ts-manuel/iMX6-Demo-Board/doc/MicroSD/2306141351_G-Switch-GT-TF003-H0185-01_C5155563.pdf

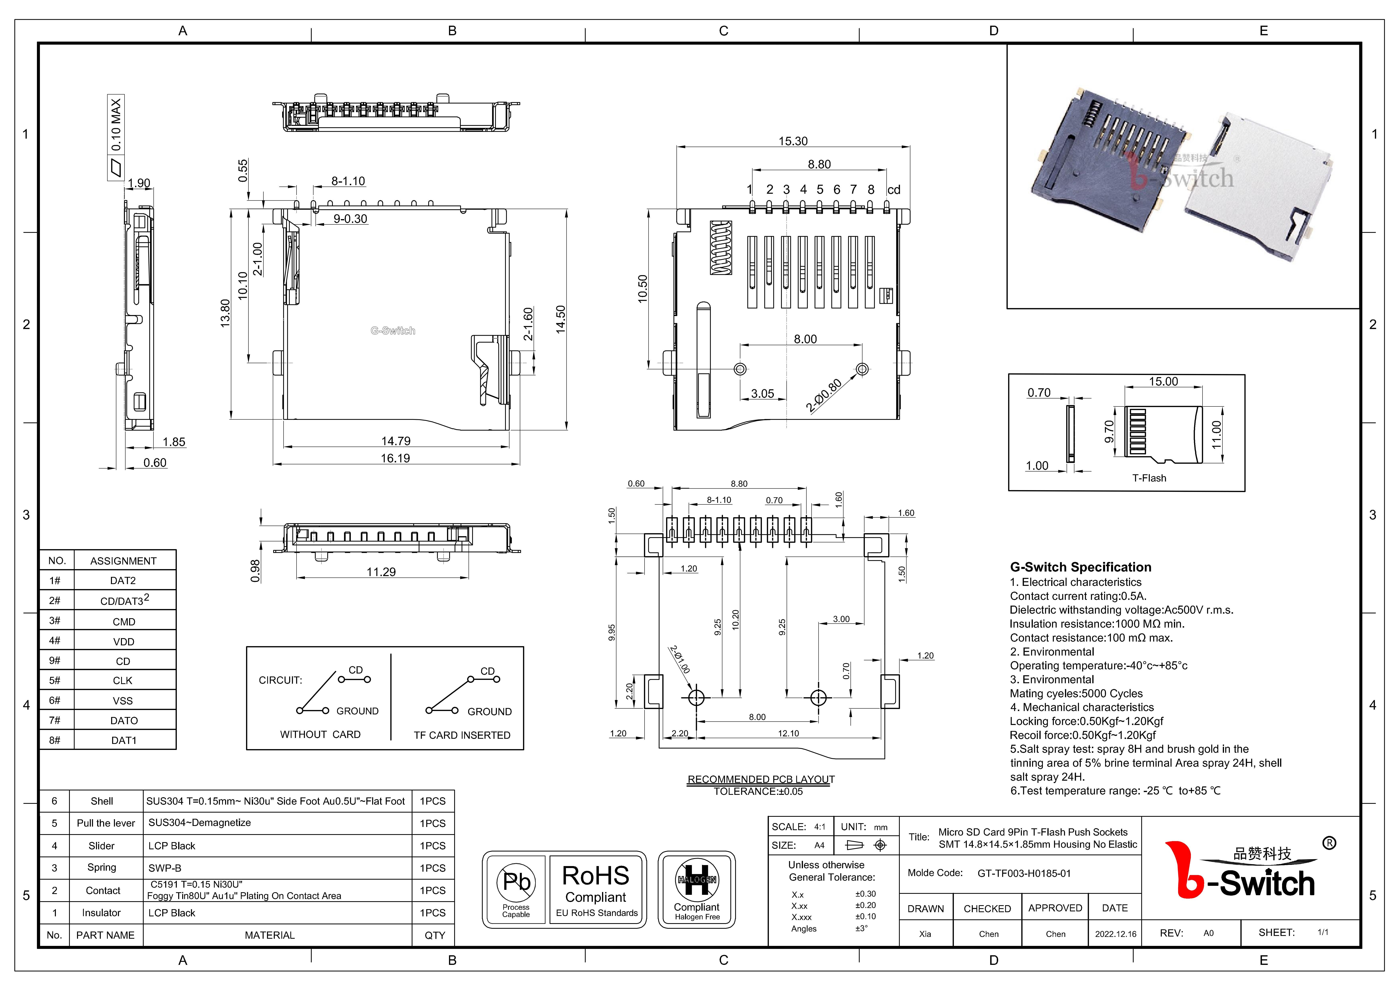
[picture p15: page 1]
