ts-manuel/iMX6-Demo-Board/doc/LCD/Alto.PNG

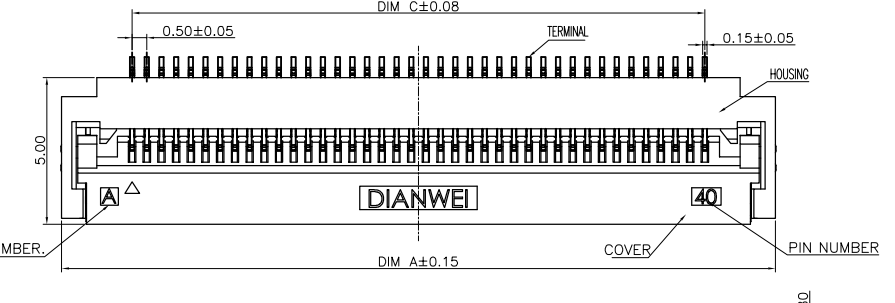
doc/LCD/Alto.PNG
