ts-manuel/iMX6-Demo-Board/doc/LCD/Basso.PNG

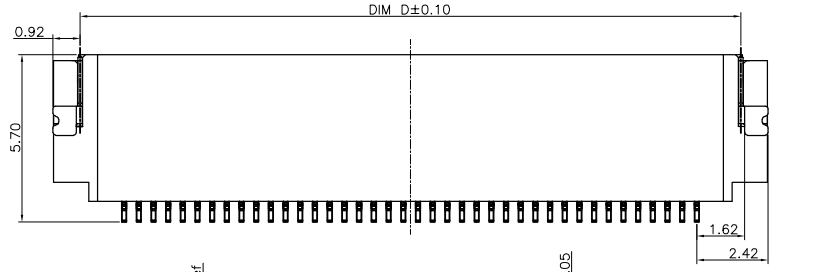
doc/LCD/Basso.PNG
