ts-manuel/iMX6-Demo-Board/kicad/images/BOOT_CONFIG.png

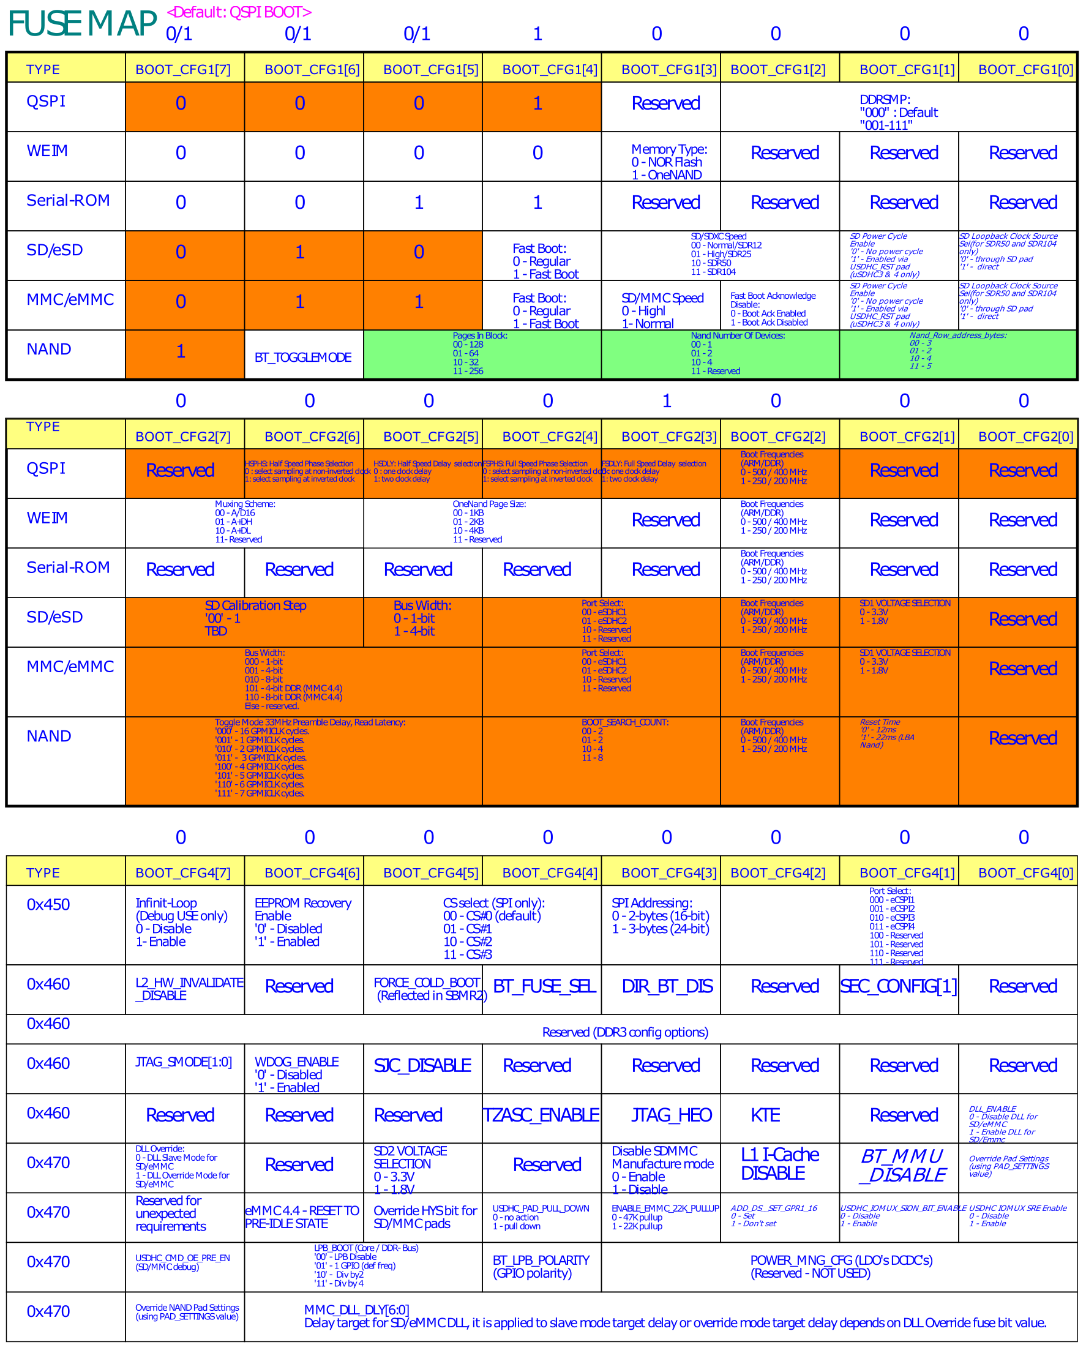
kicad/images/BOOT_CONFIG.png
