ts-manuel/iMX6-Demo-Board/kicad/images/BOOT_MODE.png

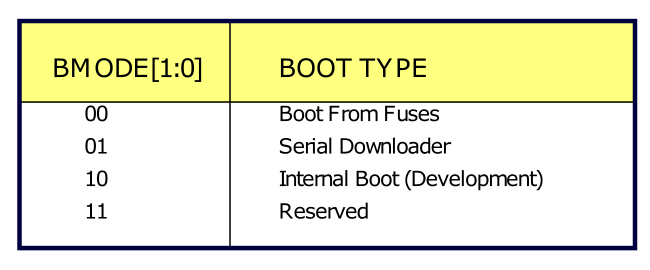
kicad/images/BOOT_MODE.png
