ts-manuel/iMX6-Demo-Board/kicad/images/BOTTOM.png

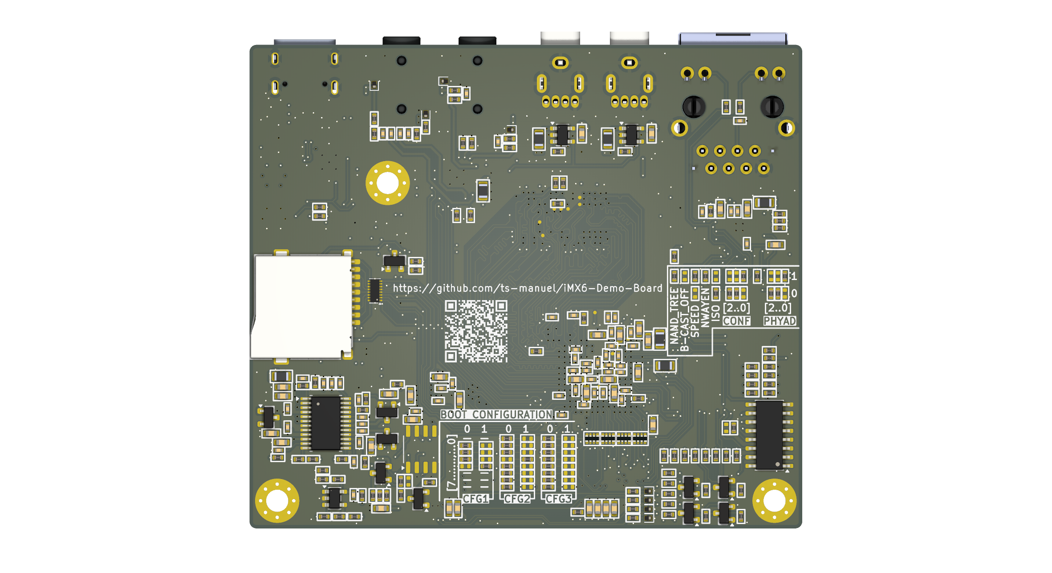
kicad/images/BOTTOM.png
