ts-manuel/iMX6-Demo-Board/kicad/images/JLC Stackup.png

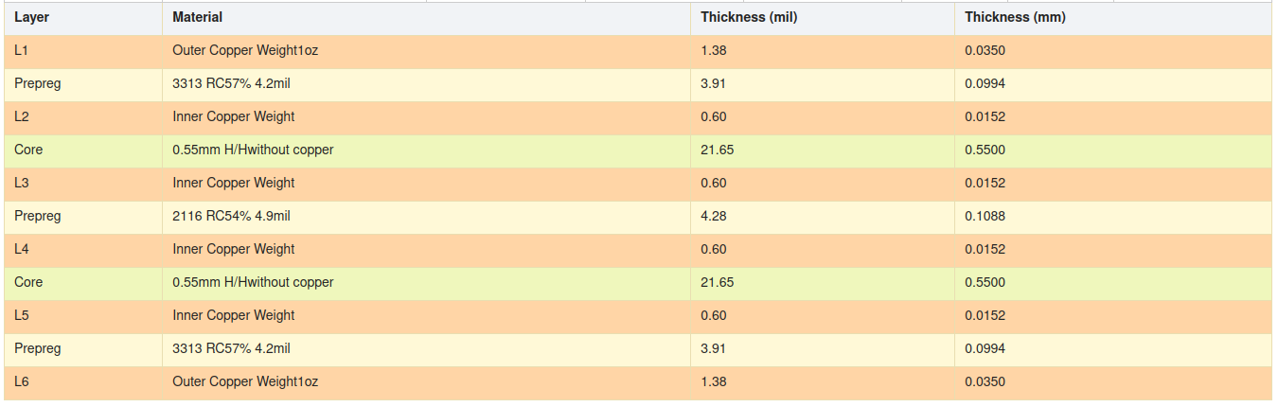
kicad/images/JLC Stackup.png
