ts-manuel/iMX6-Demo-Board/kicad/images/JLC-Impedance-Calculator.png

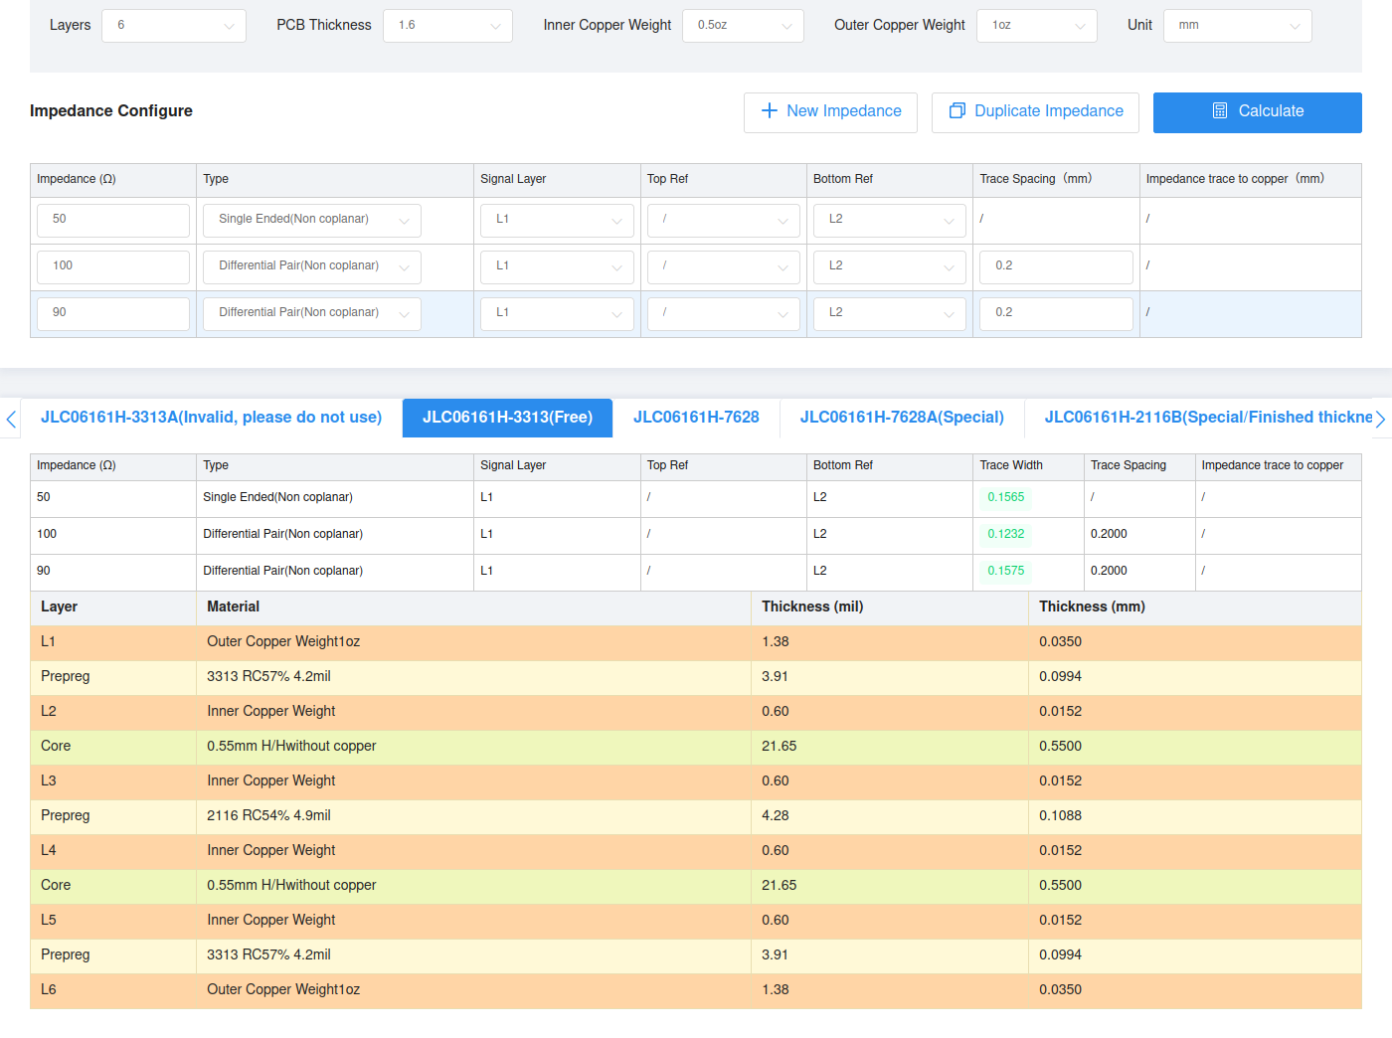
kicad/images/JLC-Impedance-Calculator.png
