ts-manuel/iMX6-Demo-Board/kicad/images/USB Load Switch Current.PNG

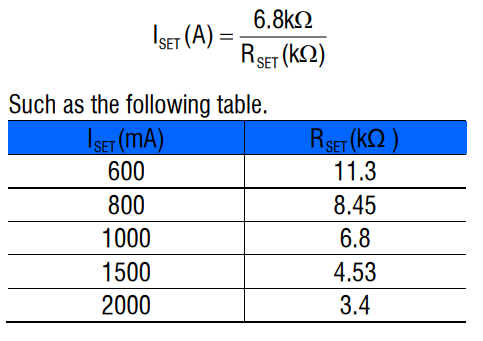
kicad/images/USB Load Switch Current.PNG
