ts-manuel/iMX6-Demo-Board/doc/iMX6/MCIM6ULL-EVK-LAYOUT.pdf

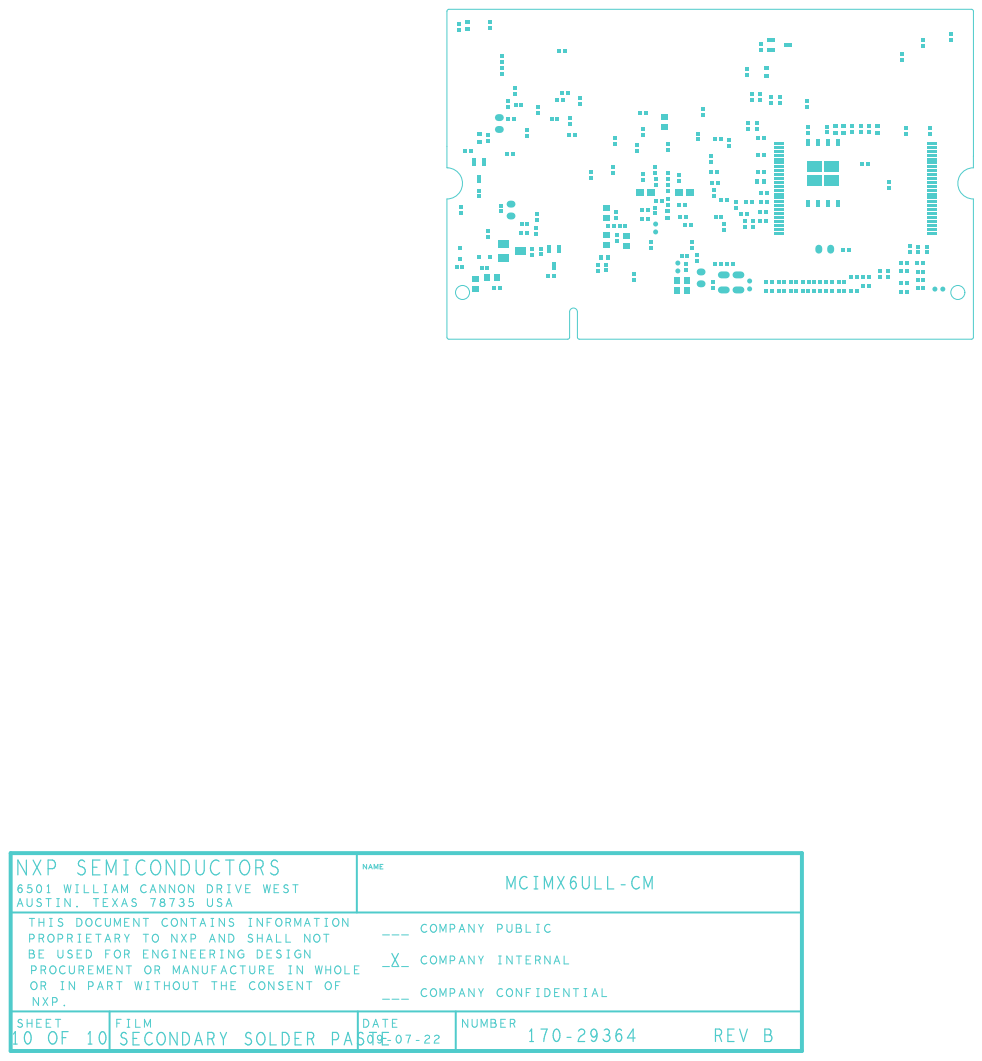
[picture p31: page 1]

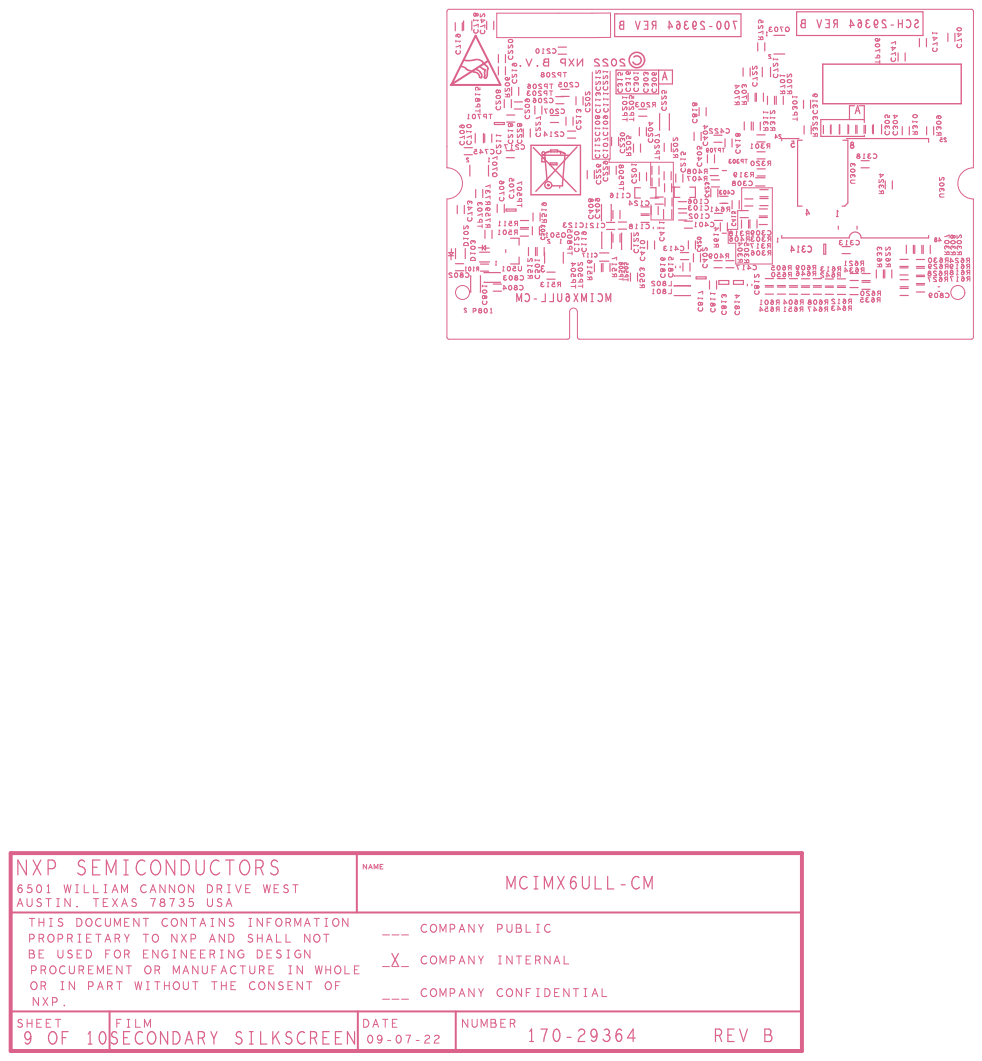
[picture p32: page 2]

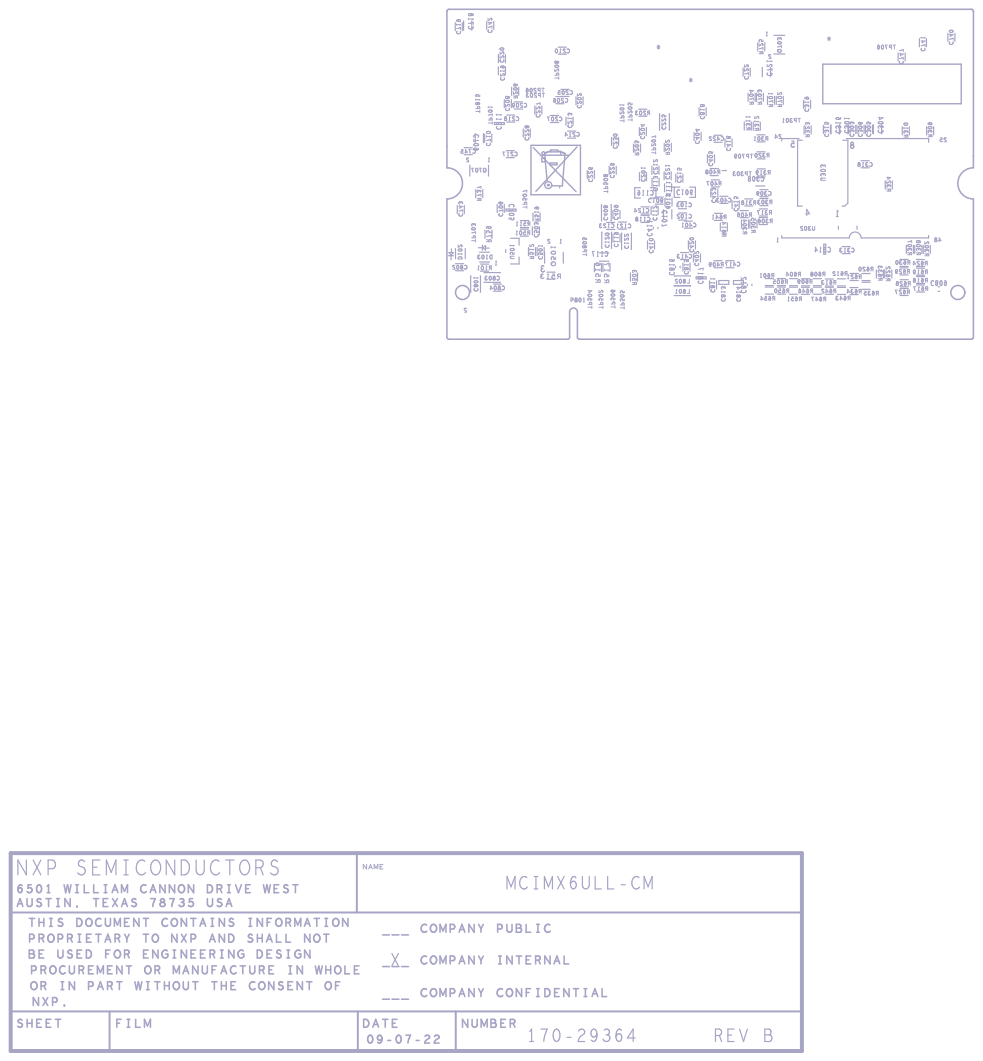
[picture p33: page 3]

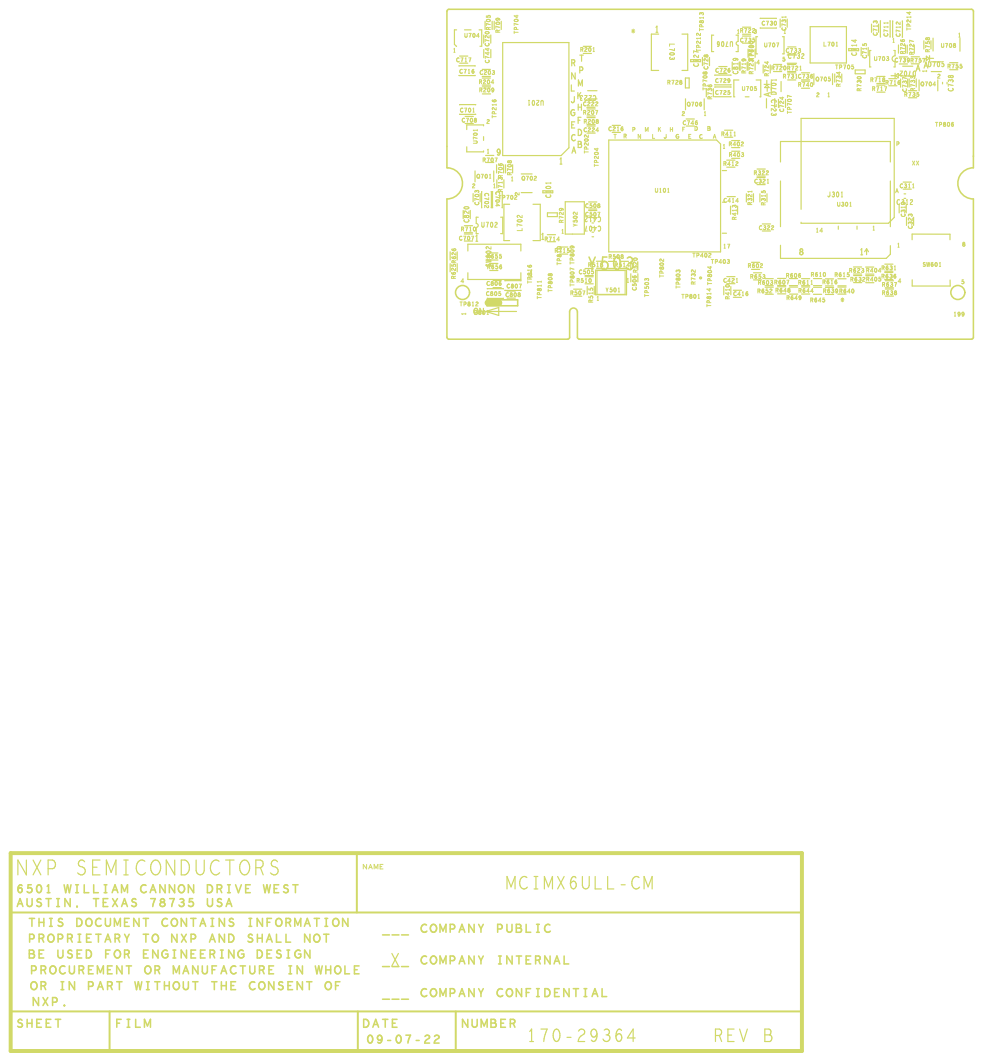
[picture p34: page 4]

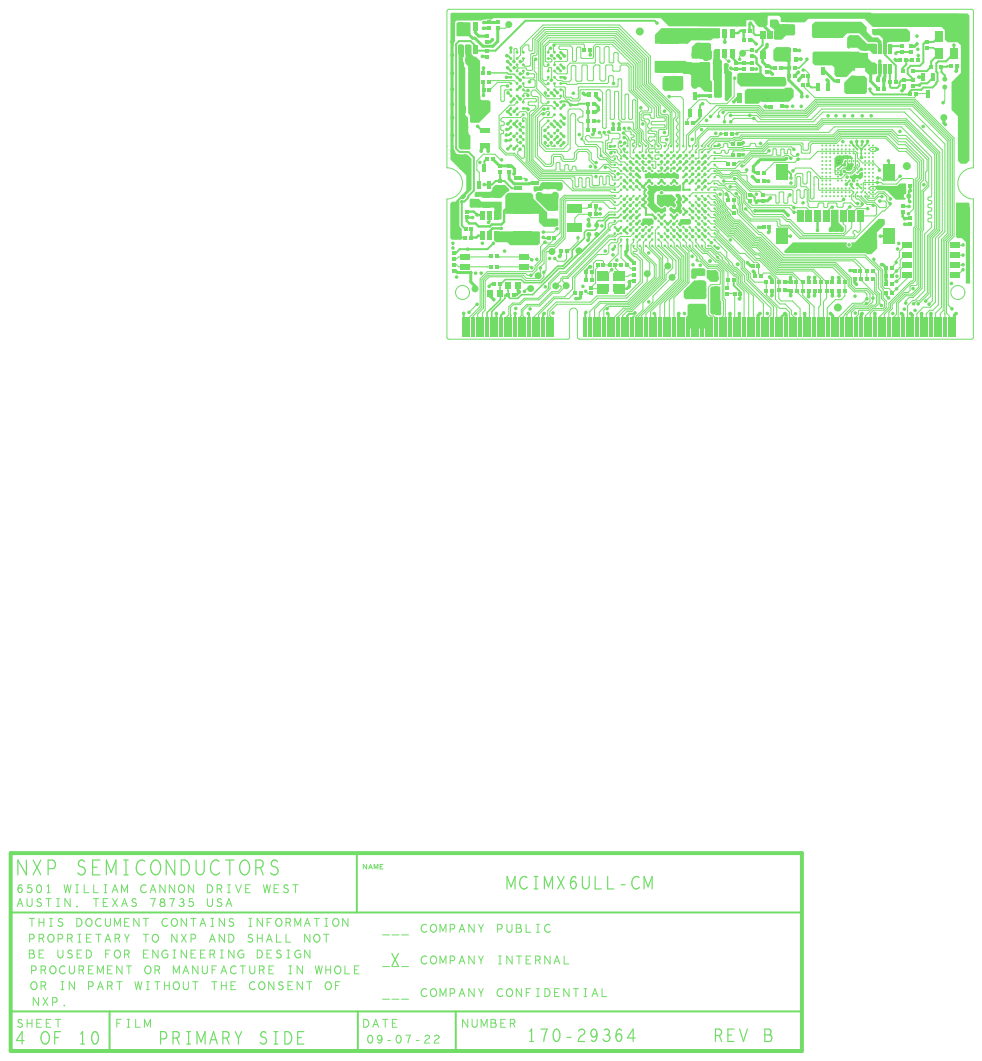
[picture p35: page 5]

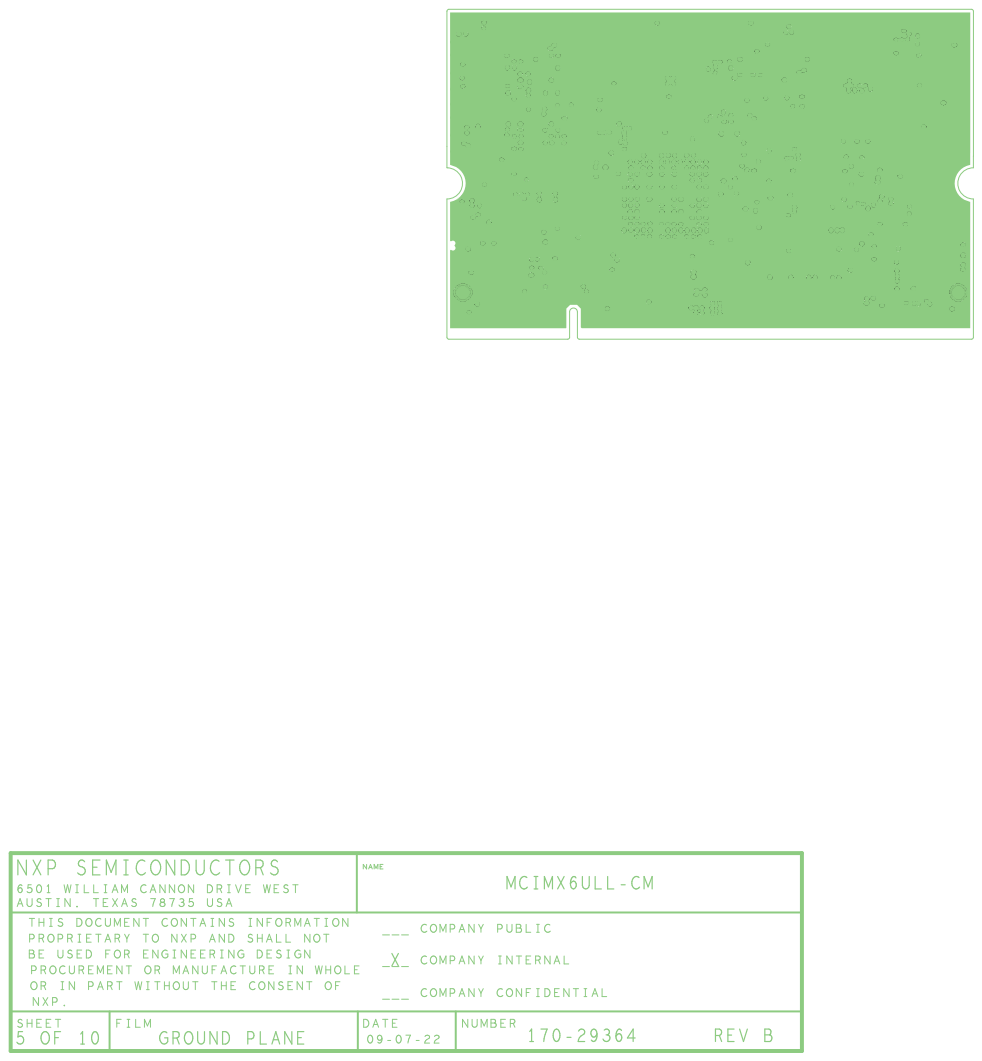
[picture p36: page 6]

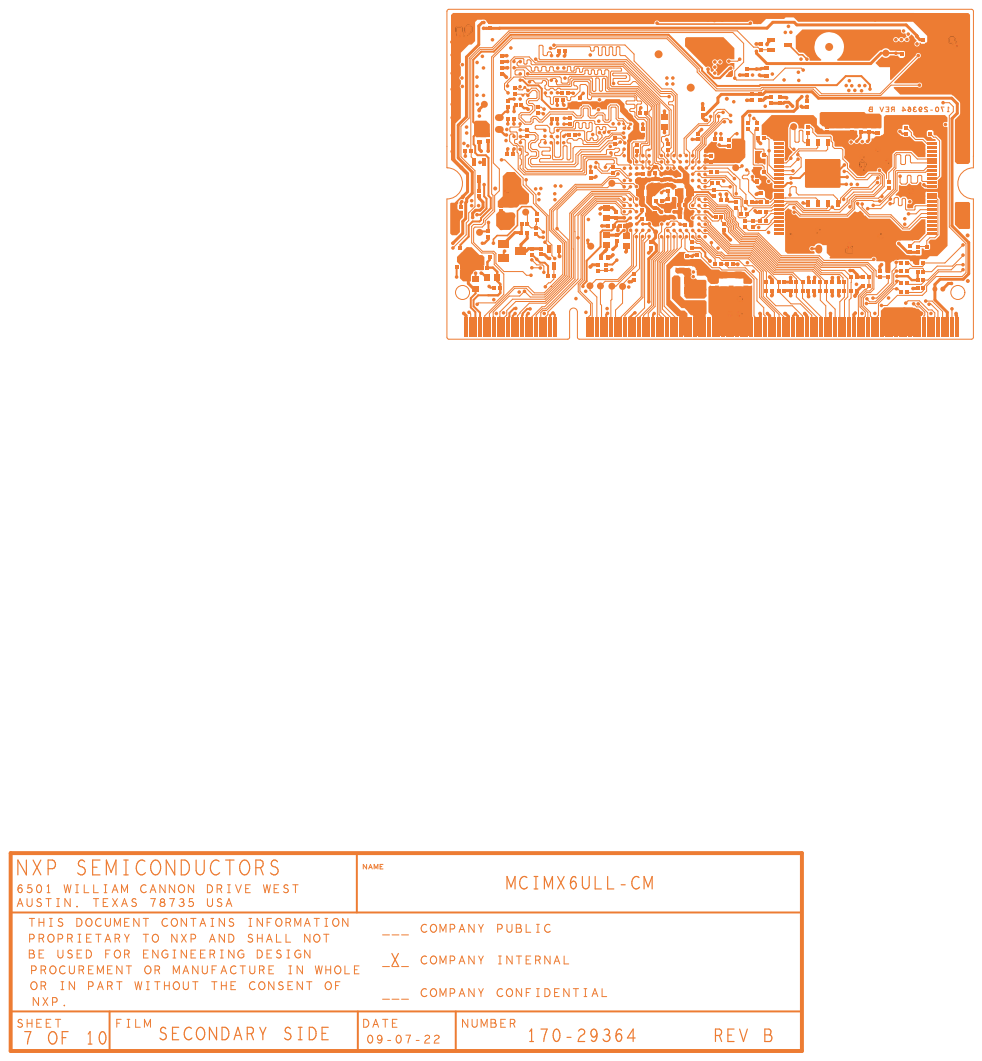
[picture p37: page 7]

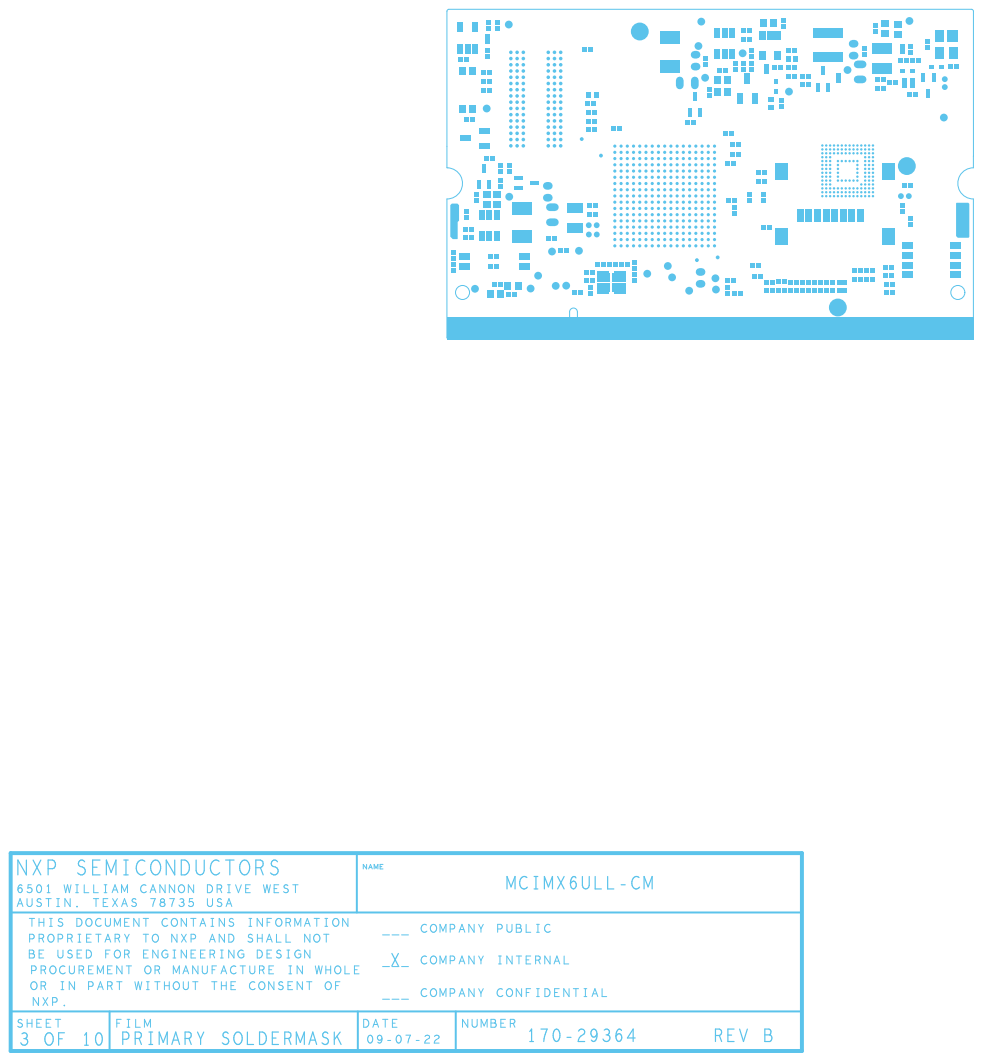
[picture p38: page 8]

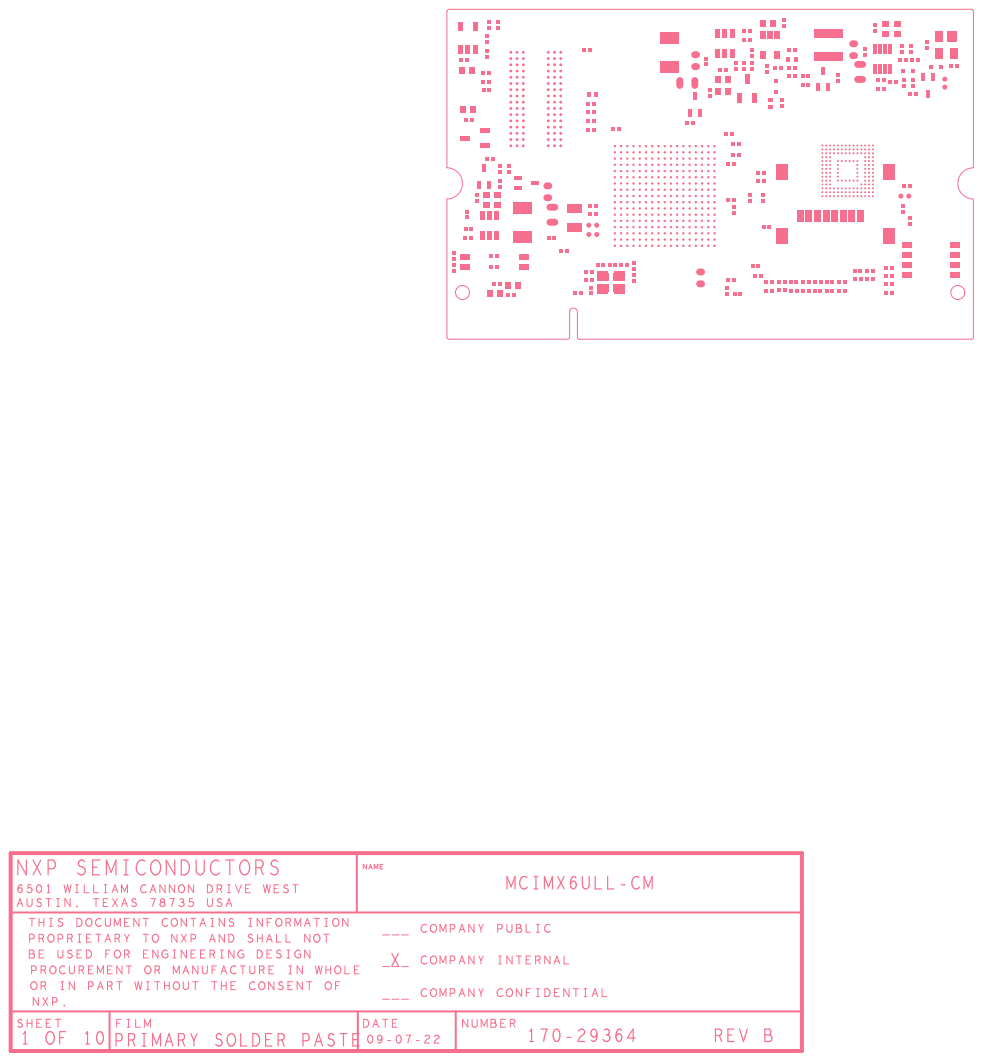
[picture p39: page 9]

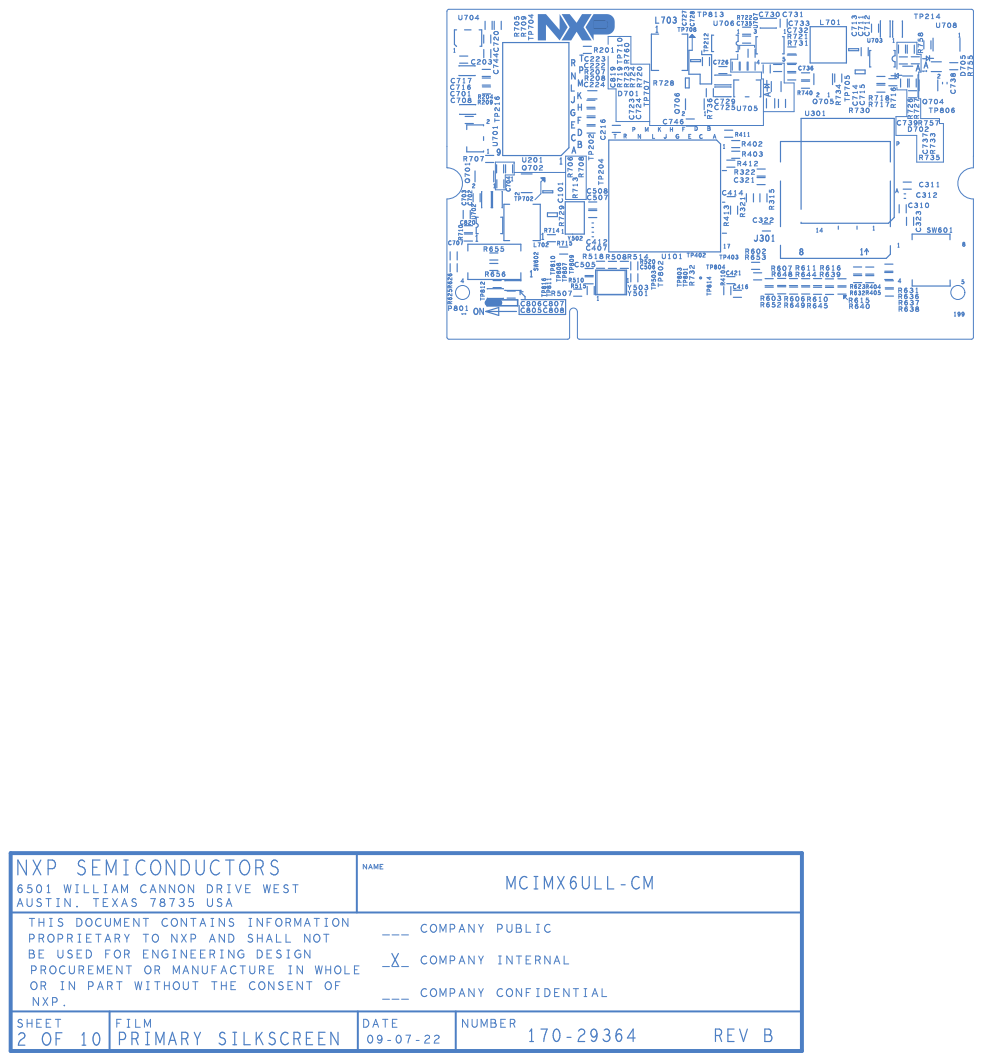
[picture p40: page 10]

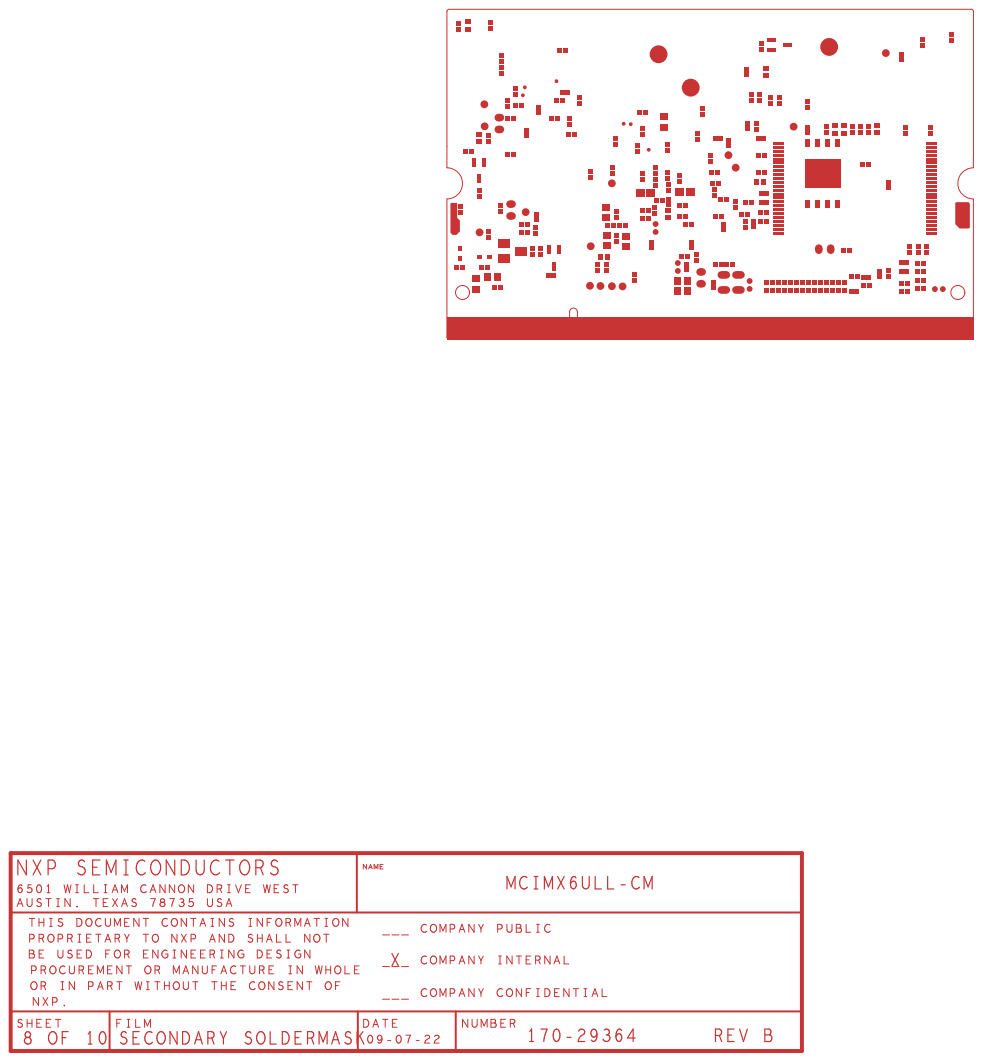
[picture p41: page 11]

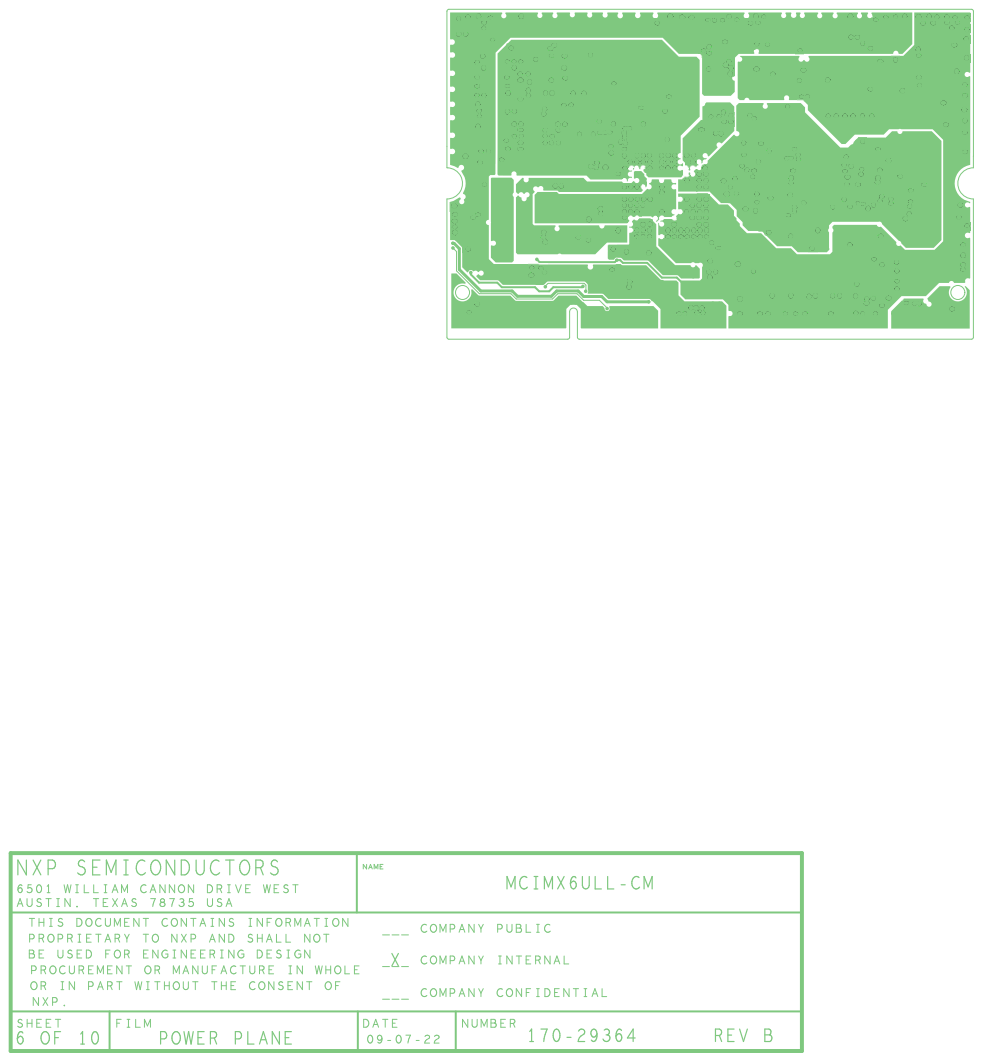
[picture p42: page 12]
