ts-manuel/iMX6-Demo-Board/ltspice/boost/boost.asc

C1: cap; 1µ
C2: cap; 2.2µ
C3: cap; 22µ
C4: cap; 2.2µ
C5: cap; 22p
C6: cap; 22p
C7: cap; 1µ
C8: cap; 1µ
C9: cap; 22µ
C10: cap; 2.2µ
C11: cap; 4.4µ
C12: cap; 22p
C13: cap; 2.2µ
C14: cap; 22p
C15: cap; 22p
D1: schottky; BAT54
D2: schottky; BAT54
D3: schottky; BAT54
D4: schottky; BAT54
L1: ind2; 6.8µ
L2: ind2; 27.2µ
L3: ind; 6.8µ
L4: ind2; 6.8µ
L5: ind2; 6.8µ
R1: res; 800
R2: res; 1.1K
R3: res; 0.1
R4: res; 80
R5: res; 1.5k
R6: res; 1.5k
R7: res; 800
R8: res; 1.1K
R9: res; 0.1
R10: res; 1.1K
R11: res; 1.5k
R12: res; 0.01
R13: res; 80
R14: res; 220
R15: res; 1.5k
S1: sw; MYSW
S2: sw; MYSW
S3: sw; MYSW
S4: sw; MYSW
S5: sw; MYSW
V1: voltage; 5V
V2: voltage; PULSE(0 1 0 1n 1n 454n 833.3n)
V3: voltage; 5V
V4: voltage; PULSE(-1 1 0 1n 1n 454n 833.3n)
V5: voltage; 5V
V6: voltage; PULSE(-1 1 0 1n 1n 536n 833.3n)
Named nets: 0, Vo2, Vo2f, Vo3, Vo3f
.model MYSW SW(Ron=0.35 Roff=1Meg Vt=.5 Vh=-.4)
.tran 0 500u 490u
K1 L1 L2 0.99
K2 L4 L5 0.95
